koopero/Plato/Plato_A2/output/Plato_A2-B_Silkscreen.png

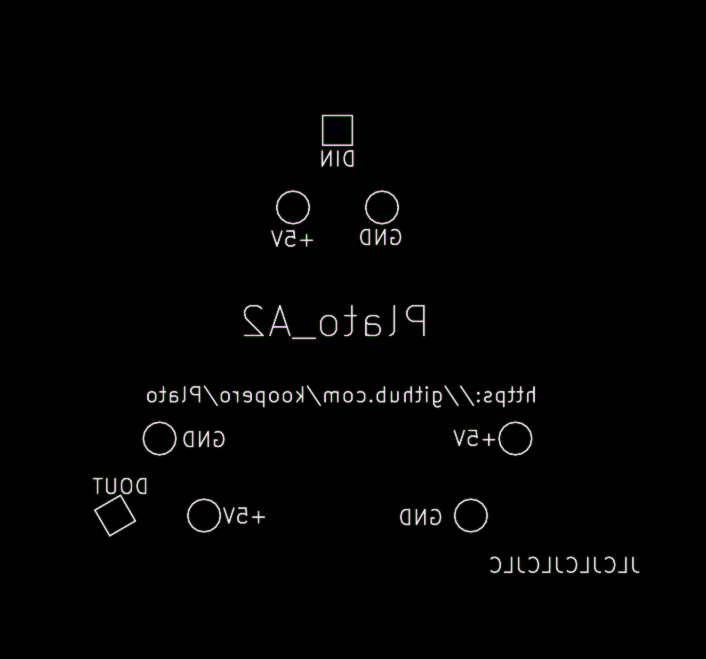
Plato_A2/output/Plato_A2-B_Silkscreen.png
