koopero/Plato/Plato_A2/output/Plato_A2-Edge.png

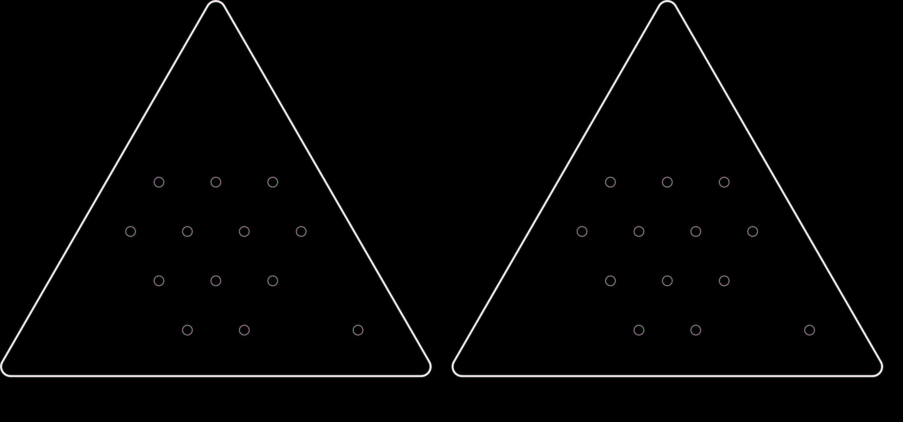
Plato_A2/output/Plato_A2-Edge.png
