koopero/Plato/Plato_A2/output/Plato_A2-Edge_Cuts.png

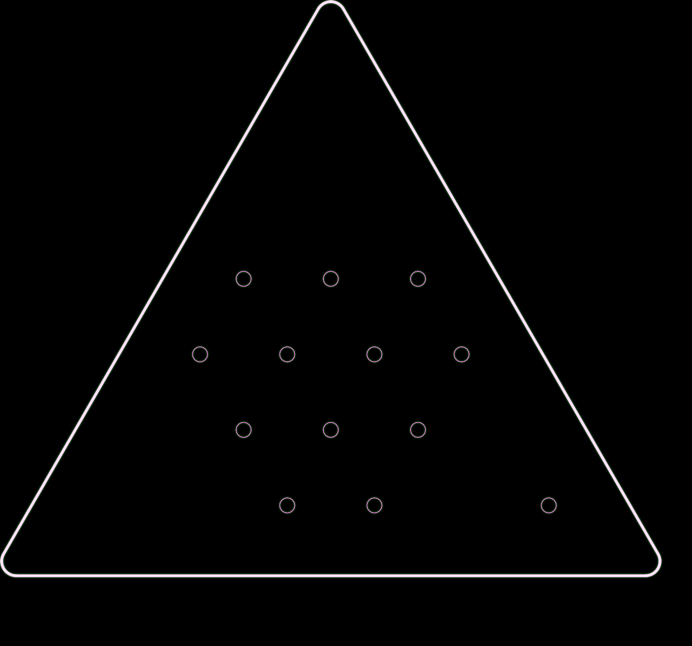
Plato_A2/output/Plato_A2-Edge_Cuts.png
