koopero/Plato/Plato_A2/output/Plato_A2-F_Cu.png

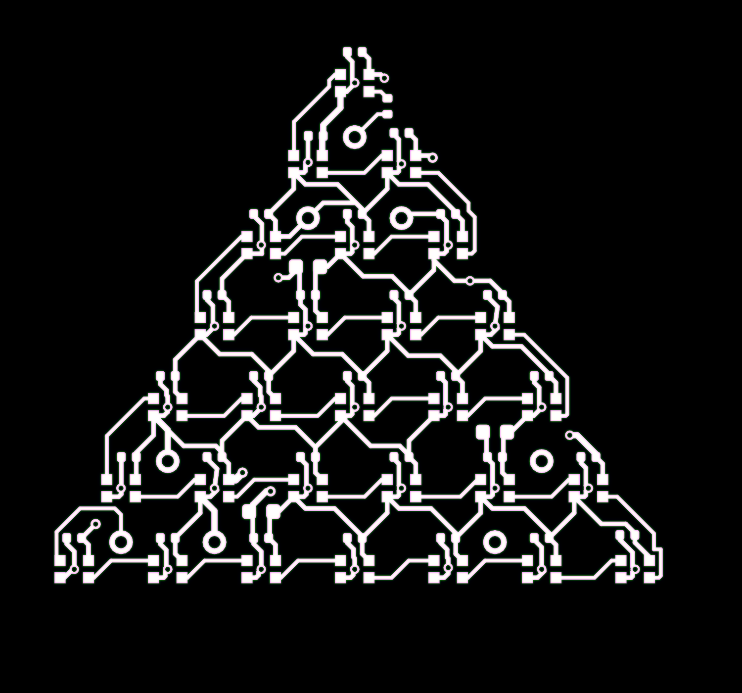
Plato_A2/output/Plato_A2-F_Cu.png
