koopero/Plato/Plato_A2/output/Plato_A2-F_Mask.png

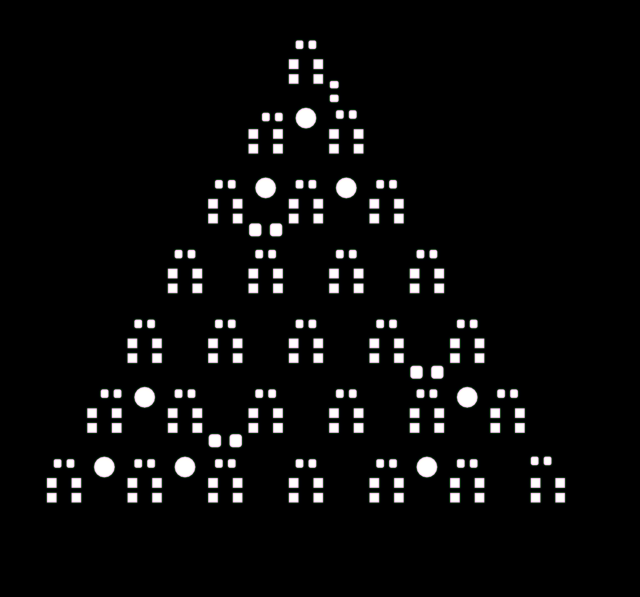
Plato_A2/output/Plato_A2-F_Mask.png
