koopero/Plato/Plato_A2/output/Plato_A2-F_Silkscreen.png

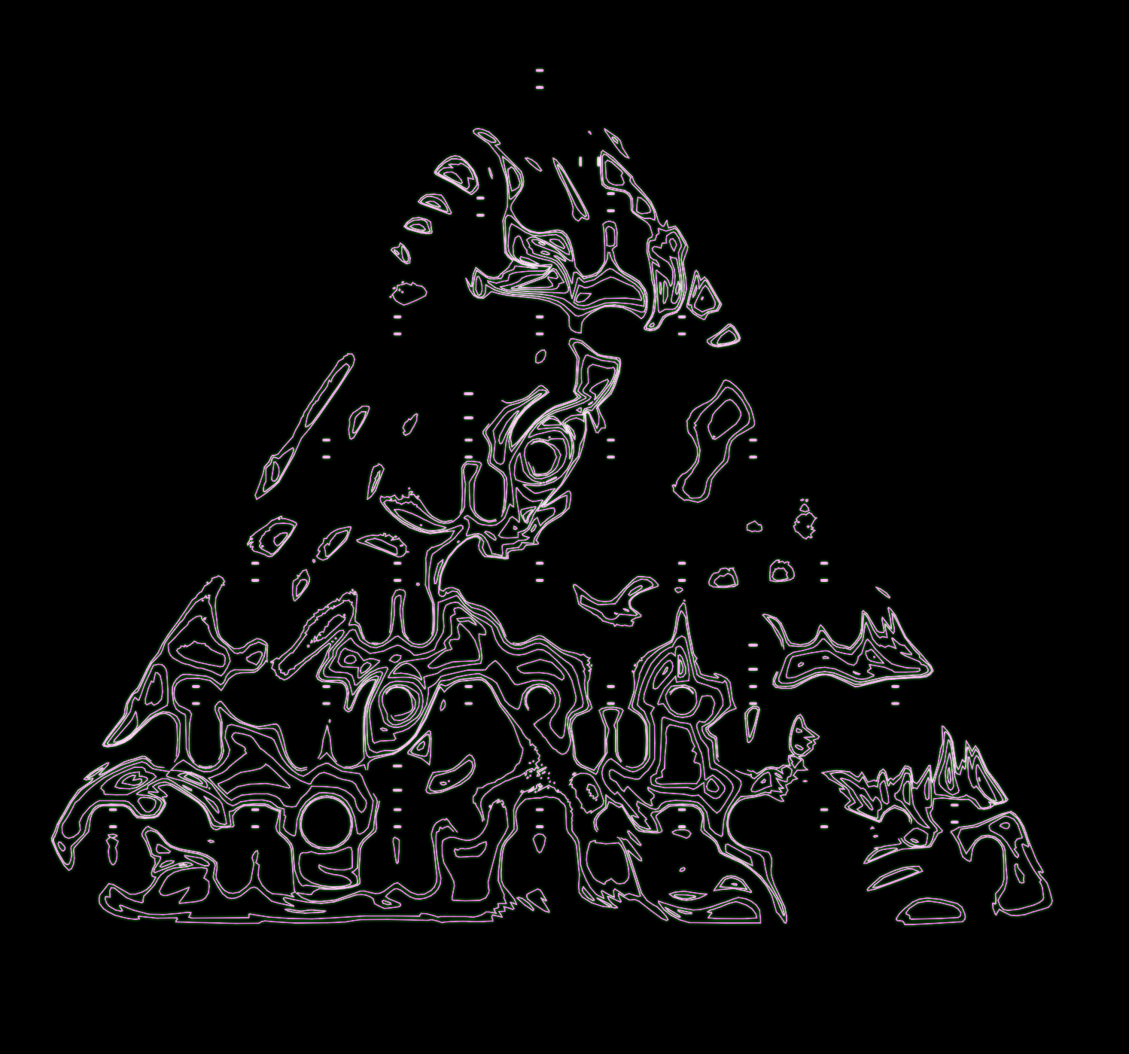
Plato_A2/output/Plato_A2-F_Silkscreen.png
