koopero/Plato/Plato_A2/output/Plato_A2-Pair-Cu.png

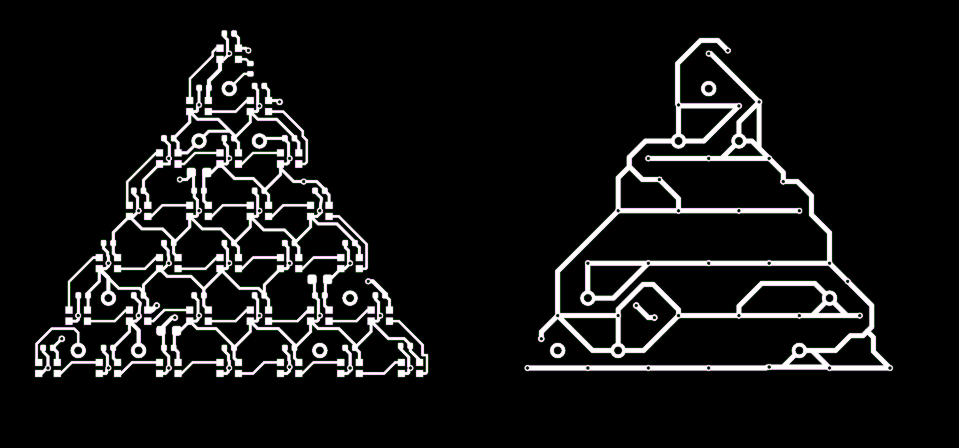
Plato_A2/output/Plato_A2-Pair-Cu.png
