koopero/Plato/Plato_A2/output/Plato_A2-Pair-Mask.png

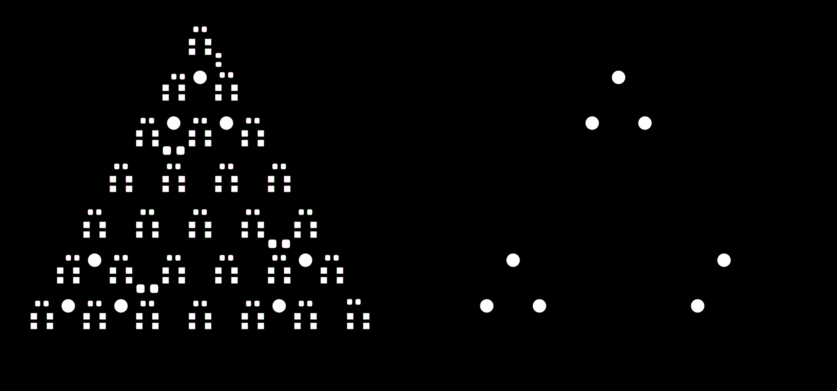
Plato_A2/output/Plato_A2-Pair-Mask.png
