koopero/Plato/Plato_A2/output/Plato_A2-Pair-Paste.png

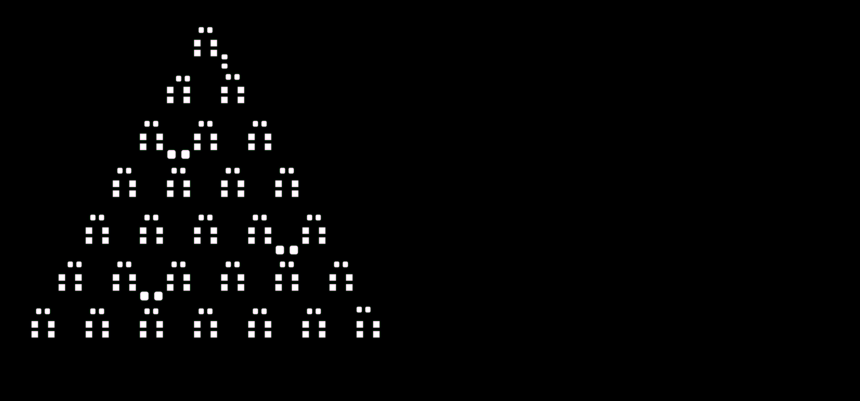
Plato_A2/output/Plato_A2-Pair-Paste.png
