koopero/Plato/Plato_A2/output/Plato_A2-Pair-Silkscreen.png

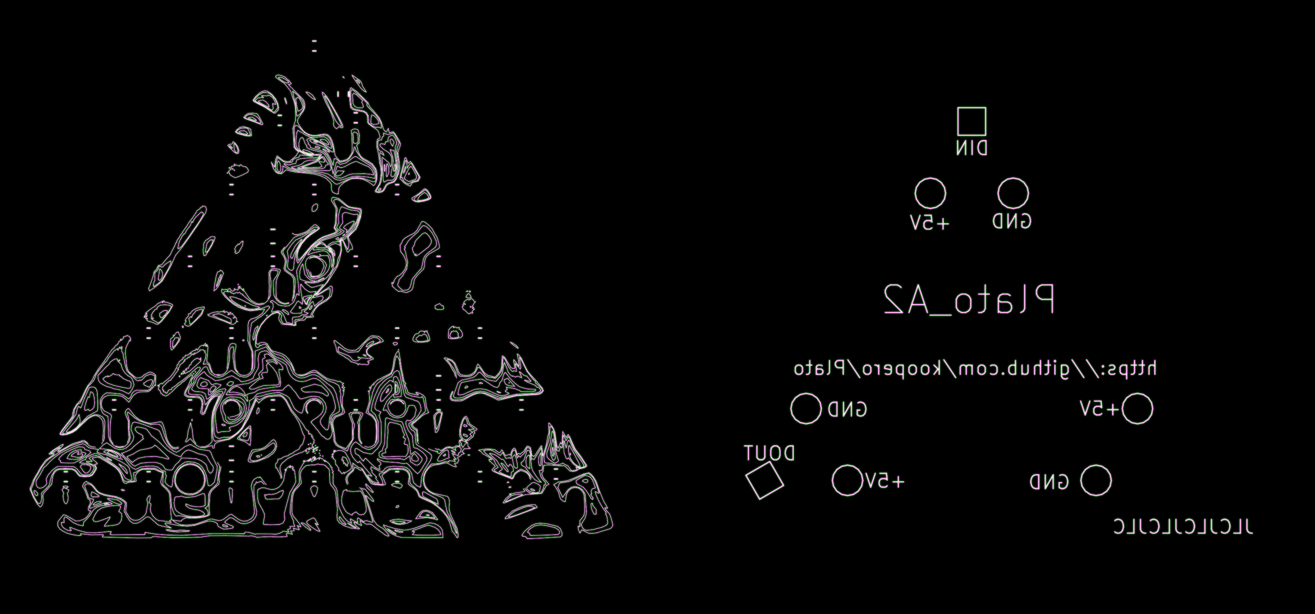
Plato_A2/output/Plato_A2-Pair-Silkscreen.png
