koopero/Plato/Plato_A2/output/Plato_A2.scad

include <./Plato_A2_Board.scad>;
   led(0.0, 20.784609690826528, 1.0);
   led(-3.0, 15.588457268119896, 1.0);
   led(3.0, 15.588457268119896, 1.0);
   led(6.0, 10.392304845413264, 1.0);
   led(0.0, 10.392304845413264, 1.0);
   led(-6.0, 10.392304845413264, 1.0);
   led(-9.0, 5.196152422706632, 1.0);
   led(-3.0, 5.196152422706632, 1.0);
   led(3.0, 5.196152422706632, 1.0);
   led(9.0, 5.196152422706632, 1.0);
   led(12.0, 0.0, 1.0);
   led(6.0, 0.0, 1.0);
   led(0.0, 0.0, 1.0);
   led(-6.0, 0.0, 1.0);
   led(-12.0, 0.0, 1.0);
   led(-15.0, -5.196152422706632, 1.0);
   led(-9.0, -5.196152422706632, 1.0);
   led(-3.0, -5.196152422706632, 1.0);
   led(3.0, -5.196152422706632, 1.0);
   led(9.0, -5.196152422706632, 1.0);
   led(15.0, -5.196152422706632, 1.0);
   led(18.0, -10.392304845413264, 1.0);
   led(12.0, -10.392304845413264, 1.0);
   led(6.0, -10.392304845413264, 1.0);
   led(0.0, -10.392304845413264, 1.0);
   led(-6.0, -10.392304845413264, 1.0);
   led(-12.0, -10.392304845413264, 1.0);
   led(-18.0, -10.392304845413264, 1.0);
